panovvv/esp8266-lighting-controllers/esp12_rgbcct_led_strip_controller/pcb/renders/02_no_raytrace_back.png

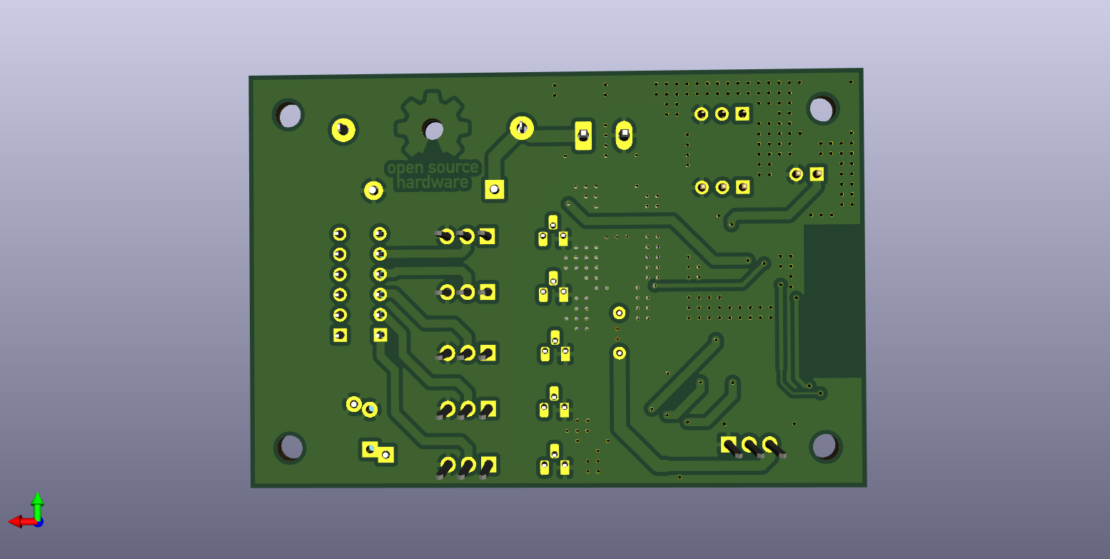
esp12_rgbcct_led_strip_controller/pcb/renders/02_no_raytrace_back.png
