panovvv/esp8266-lighting-controllers/esp12_rgbcct_led_strip_controller/pcb/renders/05_no_raytrace_left_180deg.png

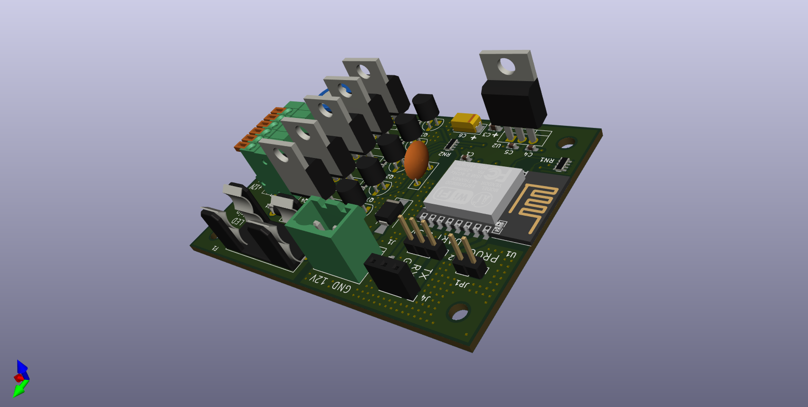
esp12_rgbcct_led_strip_controller/pcb/renders/05_no_raytrace_left_180deg.png
