panovvv/esp8266-lighting-controllers/esp12_rgbcct_led_strip_controller/pcb/renders/06_no_raytrace_right_180deg.png

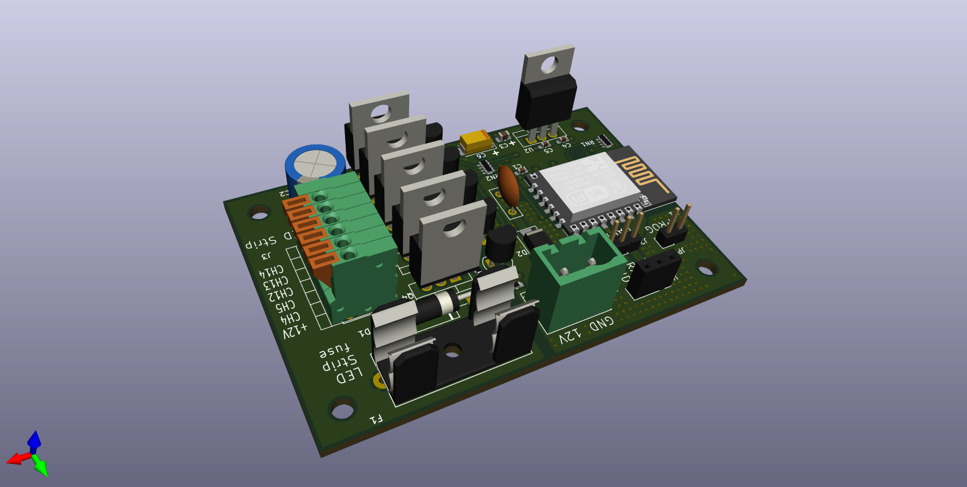
esp12_rgbcct_led_strip_controller/pcb/renders/06_no_raytrace_right_180deg.png
