panovvv/esp8266-lighting-controllers/esp12_rgbcct_led_strip_controller/pcb/renders/16_enclosure_waterproof_bottom.png

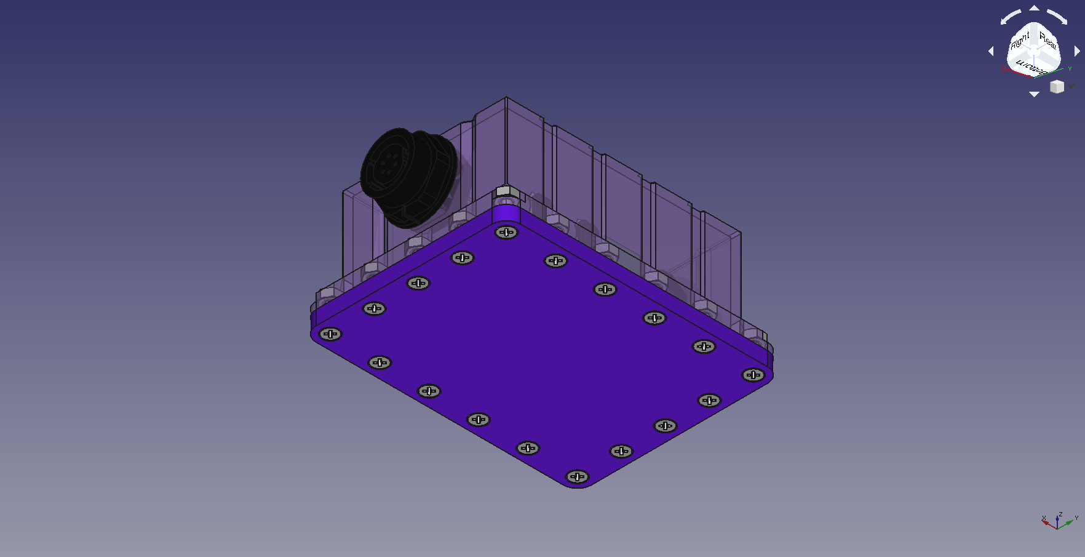
esp12_rgbcct_led_strip_controller/pcb/renders/16_enclosure_waterproof_bottom.png
