panovvv/esp8266-lighting-controllers/esp01_neopixel_controller/esp01_neopixel_controller.sch

## KiCad design esp01_neopixel_controller/esp01_neopixel_controller.sch (2020-03-27)

Schematic: esp01_neopixel_controller.sch

Parts:
C1: 470u
C2: 10u
C3, C4: 100n
C5: 100u
D1: P6KE16A; D_DO-201AE_P15.24mm_Horizontal
F1: PTC 0.5A
J1: 5V
J2: FTDI connector
J3: WS2812
JP1: PROG
R1, R2, R3, R4: 10k
U1: LM1117-3.3
U2: ESP-01
